blackstripes/Ignitron/docs/PROJECT_PLAN.md

# Spark Foot Controller Project Plan

This fork is being used as the software base for a standalone DIY foot controller for Positive Grid Spark amps, with the Spark 2 as the primary target. The goal is a polished, no-phone/no-computer playing experience while preserving Ignitron's proven Spark BLE/protocol work.

## Current status

The authoritative development branch is `main`. New Codex and Astra sessions
must start from `main`. `feature/headless-serial-cli` is historical branch
history and is retained temporarily for rollback/reference only.

`main` contains the `panelan-lvgl-controller` touchscreen controller path used
to exercise the Spark protocol without the legacy buttons, LEDs, or OLED.
Hardware verification now covers PanelLan display/touch, direct Spark BLE,
Home/Preset and confirmed FX actions, Device identity/serial, reconnect, and
the Spark 2 native tuner (external observation plus display entry/exit and
fresh note/cents rendering). Spark 2 preset and FX core reliability have both
passed 500-action acceptance. Current priority is completing the remaining mini
displays, switches, wiring, power/decoupling, and physical controller
integration. FX confirmation latency optimization is deliberately deferred until
after that hardware/UI bring-up; see
[DEFERRED_FX_LATENCY_OPTIMIZATION.md](DEFERRED_FX_LATENCY_OPTIMIZATION.md).
Spark 2 internal looper remains unimplemented and follows the hardware priority.
See [PANELAN_PROTOTYPE.md](PANELAN_PROTOTYPE.md) and
[CODEX_HANDOFF.md](../CODEX_HANDOFF.md) for live status.

The upstream Ignitron code is built around classic ESP32 targets and uses NimBLE for Spark communication. The final controller hardware will be ESP32-S3-based, so there will be a deliberate port step rather than assuming the stock target is drop-in compatible.

## Product goal

Build a standalone floor controller that connects directly to a Spark 2 over BLE and provides:

- Preset/bank selection
- Individual FX toggles
- Spark 2 internal looper control
- Tuner UI
- Tap tempo
- Dynamic per-switch labels/status
- A larger contextual main display
- Optional expression pedal inputs later
- USB power first; battery power can be added later

The finished controller should not require the Spark mobile app for normal Spark 2 use.

## Hardware direction

### Main controller/display board

The intended prototype/final controller board has now been positively identified from the PCB markings as:

- **PanelLan ZX2D80CE02S V1.0**
- PanelLan board family / model: **SC05_X / ZX2D80CE02S**
- Module marking: **WT32-S3-WROVER**
- MCU family: **ESP32-S3**
- Main display: **2.8-inch 240x320 IPS TFT**
- Main LCD controller: **ST7789**
- LCD bus: **8-bit 8080 parallel**, not SPI
- Touch: **FT5x06 capacitive touch**
- Existing PanelLan Arduino support is available and is based on **LovyanGFX**

Important implementation note: **do not treat the built-in display as a generic SPI ST7789 module.** Start from the known PanelLan `SC05_X` / `ZX2D80CE02S` board configuration and vendor/library support rather than inventing a pin map from scratch.

The rear expansion connector is visibly labeled:

```text
+5V
GND
IO10
IO11
IO12
IO13
IO14
IO21
```

That gives six user-accessible GPIOs for the pedal hardware. The current tentative allocation is:

```text
IO10  Mini TFT SPI MOSI
IO11  Mini TFT SPI SCLK
IO12  I2C SDA
IO13  I2C SCL
IO14  Shared mini-TFT DC
IO21  Spare / reserve
```

On I2C, the current plan is:

```text
IO12/IO13
   |-- MCP23017  -> footswitch inputs and/or six mini-TFT CS lines
   `-- ADS1115   -> future expression pedal inputs
```

The six ST7735S mini TFTs should share SPI clock/data. The MCP23017 can drive six individual CS lines directly unless a decoder later proves simpler in software/hardware.

The board's built-in display/touch use their own onboard connections, so the external IO10-IO14/IO21 pins are intended to remain available for external hardware. Still verify all details against the exact vendor board support files during the S3 port.

Before finalizing firmware pin definitions, Codex should:

- Pull the exact PanelLan SC05_X / ZX2D80CE02S board config from the maintained support package.
- Verify flash/PSRAM size and board build flags from the actual library/example.
- Verify touch-controller pins and LCD bus config from the vendor/library source.
- Confirm USB serial behavior on the physical board.
- Confirm the external IO connector pin assignments electrically before wiring all peripherals.
- Keep board-specific pin definitions isolated in a dedicated hardware config.

### Per-switch displays

Six purchased modules:

- 0.96-inch IPS TFT
- 80x160 / 160x80
- ST7735S
- SPI
- 7-pin breakout
- 3.3 V

These are intended to sit above the six primary footswitches and dynamically show labels such as `P1`, `DELAY`, `REC/DUB`, `UNDO`, etc.

Plan to share SPI clock/data across all six displays and give each display independent selection. Candidate approaches:

1. MCP23017 drives six CS signals directly.
2. A 3-to-8 active-low decoder drives CS lines, with selection controlled either by native GPIO or the MCP23017.

Given the confirmed six-pin external GPIO budget on the PanelLan board, direct CS control from the MCP23017 is currently the preferred starting point. The mini displays should be treated as write-only if possible; no MISO is expected to be required.

### Footswitches

Six purchased main switches:

- DaierTek PBS-24-302 style
- Momentary SPST
- 12 mm metal stomp switches

Current UX direction is **six primary switches plus two utility switches**:

- `MODE`
- `TAP / TUNER`

The exact utility-switch hardware can be selected later.

### GPIO expansion

A Waveshare MCP23017 breakout is planned for switch inputs and/or display chip selects.

Preferred switch electrical model:

- MCP23017 at 3.3 V
- Inputs use pull-ups
- Switches connect input to GND
- HIGH = idle, LOW = pressed

Interrupt support is optional; simple polling is acceptable initially.

### Power

USB 5 V is the initial power source.

Purchased 5 V -> 3.3 V mini buck modules can supply the six small TFTs and other 3.3 V peripherals. Verify actual output voltage with a meter before connecting displays. Do not assume the advertised current rating is a safe continuous rating without testing.

Add sensible local/bulk decoupling. Battery support is intentionally deferred until the USB-powered prototype is stable.

### Expression pedals — later phase

Possible future hardware:

- ADS1115 on I2C
- Two TRS expression jacks
- Series resistance/filtering/protection
- Tip/ring polarity configurable because expression pedals are not universal

Important: **continuous volume/wah control is not yet proven at the Spark protocol level.** Ignitron exposes parameter-change mechanisms, but the correct live parameter mapping still needs to be identified before expression support is promised.

## Physical UX direction

Use the Line 6 HX Stomp XL as inspiration for visual hierarchy and foot-control ergonomics, but keep the controller simpler.

Preferred layout: a **3 x 2 matrix of six primary switches** with a mini TFT above each switch, a larger main screen above the grid, and two dedicated utility switches.

Proposed behavior:

### Preset mode

```text
P1       P2       P3
P4       BANK-    BANK+
```

### FX mode

```text
GATE     COMP/WAH DRIVE
MOD      DELAY    REVERB
```

### Looper mode

Example only; final behavior should follow verified Spark 2 looper functions:

```text
REC/DUB  PLAY/STOP  UNDO/REDO
CLEAR    STATUS/TAP CONFIG
```

`MODE` should cycle among the useful controller modes without relying heavily on long presses.

`TAP / TUNER` should preferably use:

- short press: tap tempo
- long press: tuner

The main display should show context rather than simply duplicate the mini labels: active bank/preset, preset name, connection state, active FX, looper state, tuner, and later expression state.

No rotary encoders are planned initially. The main screen is touch-capable and the Spark app remains available for deep tone editing. Add an encoder only if a concrete interaction later justifies it.

## Enclosure direction

Prefer a 3D-printed enclosure rather than a hand-cut metal faceplate.

Target a compact sloped enclosure that can fit on a Bambu P1P 256 x 256 mm build plate. A rough concept of 9-10 inches wide by 6-7 inches deep has been discussed, but **final CAD dimensions must wait for physical measurement of all boards and switches.**

Design considerations:

- PETG or ASA preferred over brittle PLA for the final unit
- Reinforced/ribbed top around stomp switches
- Heat-set inserts for serviceable assembly
- Recess/protect all displays so stomp loads never transfer into PCBs
- Keep wiring/service access practical

Before CAD, make a full-scale cardboard/paper layout and physically test foot spacing.

## Software architecture direction

The finished code should avoid mixing Spark protocol logic, UI rendering, and physical button handling.

Preferred separation:

1. **Spark transport/protocol layer**
   - Preserve Ignitron's working BLE/protocol implementation as much as possible.
   - Avoid unnecessary rewrites.

2. **Controller state layer**
   - Amp connected/disconnected
   - Amp identity
   - Bank/preset and preset name
   - FX state
   - Looper state/config
   - Tuner note/offset/state
   - Tap/BPM
   - Future expression state

3. **Input/action layer**
   - Footswitch events
   - Touch events
   - Serial CLI commands
   - Maps user actions onto protocol operations

4. **Renderer layer**
   - Main TFT renderer
   - Six mini-TFT renderer(s)
   - Headless/serial renderer for development/debugging

5. **Hardware abstraction/configuration**
   - Board pin definitions
   - Display bus/select implementation
   - MCP23017
   - Future ADS1115

Keep the serial CLI in the finished firmware as a development/service interface even after physical controls are working.

## Serial/headless development mode

The serial CLI is an existing service/diagnostic path. Keep it available while
touch and future physical controls mature; it is the first place to probe an
unverified Spark capability without inventing UI behavior.

Desired serial commands include at least:

```text
help
status
amp
refresh
preset 1
preset 2
preset 3
preset 4
bank up
bank down
fx gate toggle
fx comp toggle
fx drive toggle
fx mod toggle
fx delay toggle
fx reverb toggle
tuner on
tuner off
tap
loop rec
loop dub
loop play
loop stop
loop undo
loop redo
loop clear
```

The serial interface should return useful success/failure/status output and should not block the BLE processing loop.

Headless mode must not require an OLED, LEDs, or physical buttons to boot. Stock Ignitron display initialization can halt forever when the expected OLED is absent, so display initialization must be bypassed cleanly in this mode.

## Spark 2 functional target

The Spark 2 is the primary supported amp for this project.

Current functional checkpoint after a successful BLE connection:

1. Read amp identity / serial / current preset state — verified.
2. Change hardware preset — verified.
3. Read/update FX state — verified for the PanelLan action path.
4. Enter/exit tuner and display fresh note/cents data — verified on Spark 2.
5. Exercise Spark 2 internal looper commands/status — pending.
6. Verify reconnect behavior after amp/controller restart — ongoing matrix.

The controller should use Ignitron's normal APP-mode/direct BLE path for Spark 2.

## Spark NEO Core investigation

Ignitron explicitly supports the original Spark NEO. NEO support was added before Spark NEO Core was released.

Positive Grid describes NEO and NEO Core as sharing the same amp modeling/effects/Spark app integration, while Core omits the NEO wireless transmitter feature. This makes NEO Core support plausible, but **it has not been confirmed in Ignitron and must not be treated as guaranteed.**

Once the controller can connect to Spark 2, perform a minimal NEO Core compatibility test:

1. BLE scan and identify advertised device/name/services.
2. Attempt Ignitron APP-mode connection.
3. Request serial/amp identity.
4. Request current preset.
5. Change preset.
6. Test one FX toggle.

If the NEO Core advertises a different name but uses the same Spark app protocol, add the smallest possible compatibility adjustment rather than creating a separate architecture.

## ESP32-S3 port constraints

The final controller is expected to use ESP32-S3 on the identified PanelLan ZX2D80CE02S / SC05_X board.

Important differences from classic ESP32:

- S3 supports BLE but not Bluetooth Classic.
- Direct Spark APP-mode BLE is the path we care about.
- Ignitron features relying on Bluetooth Classic serial are not a requirement for this controller.
- Review ESP-specific MAC manipulation, BLE keyboard code, core pinning/task assumptions, filesystem configuration, and library versions during the port.
- The onboard ST7789 is connected by **8-bit 8080 parallel**, so reuse the PanelLan/LovyanGFX support path rather than adapting generic SPI-ST7789 code.

Do not entangle the first S3 bring-up with all displays and switches at once.

## Archived initial development sequence

Milestones 1–5 below describe the completed initial port/LVGL rollout and are
kept for context. The active sequence is the looper-first plan in
`CODEX_HANDOFF.md` and the "Immediate Codex task" section below.

### Milestone 1 — stabilize the current headless implementation on main

- Review the current `main` implementation and its recent history.
- Build `esp32dev-headless` with PlatformIO.
- Fix compile/link issues.
- Ensure headless boot does not touch OLED/button/LED hardware.
- Ensure BLE processing is never blocked by CLI input.
- Keep upstream behavior unchanged for normal/non-headless builds where practical.

### Milestone 2 — PanelLan board bring-up

- Use the exact `ZX2D80CE02S / SC05_X` board support rather than a generic ESP32-S3 display profile.
- Run the vendor/demo firmware first.
- Confirm main TFT, FT5x06 touch, USB serial, flash/PSRAM.
- Record the exact support-package version and board config used.
- Confirm the exposed connector pins IO10, IO11, IO12, IO13, IO14, IO21.
- Create a board-specific config instead of scattering GPIO numbers through the code.

### Milestone 3 — ESP32-S3 protocol bring-up

- Get the project compiling for the exact PanelLan board.
- Start with serial + BLE only.
- Scan for Spark 2.
- Connect and run the functional target sequence above.
- Do not start custom UI work until direct Spark control is stable.

### Milestone 4 — NEO Core compatibility test

- Run the minimal NEO Core test sequence.
- Document exact findings and any code differences required.

### Milestone 5 — main display UI (completed foundation)

- Use the PanelLan/LovyanGFX support path for the onboard 2.8-inch ST7789 parallel TFT and FT5x06 touch.
- Start with connection/preset/FX/tuner/looper status.
- Keep the protocol layer independent from the graphics library.

### Milestone 6 — six mini displays + switch expander

- Mini display #1 (top-left) is now hardware-tested in the integrated controller
  using the SPI2 renderer; it follows the touchscreen Preset (`P1`) and FX
  (`GATE`) views. The GPIO bit-bang renderer remains an explicit fallback.
- Next, validate shared hardware SPI with all six ST7735S displays and provide
  each panel an independent chip-select, likely through the planned MCP23017.
- Add MCP23017 switch inputs and display selection.
- Current tentative native pins are IO10=MOSI, IO11=SCLK, IO12/13=I2C, IO14=shared DC, IO21=spare.
- Only after the electrical approach is stable should all six displays be connected.

### Milestone 7 — final interaction model

- Implement Preset / FX / Looper modes.
- Implement MODE and TAP/TUNER utilities.
- Minimize obscure long-press behavior.
- Make mini labels/state obvious from standing height.

### Milestone 8 — enclosure

- Measure actual hardware.
- Make a full-size physical layout mockup.
- CAD and print a prototype enclosure.
- Iterate ergonomics before final cosmetic print.

### Later milestone — expression inputs

- Add ADS1115/TRS hardware.
- Reverse-engineer/verify the relevant Spark live parameter mapping.
- Only then implement volume/wah behavior.

## Development rules / guardrails

- Preserve upstream Spark protocol code unless there is a demonstrated reason to change it.
- Do not claim NEO Core support until tested.
- Do not claim expression-wah support until the live parameter mapping is verified.
- Use the exact PanelLan board support for the main display/touch rather than generic assumptions.
- Keep final board pins isolated in board-specific config and verify them against the physical unit/vendor source.
- Prefer incremental hardware bring-up: one subsystem at a time.
- Keep serial diagnostics available throughout development.
- Maintain clear compile-time or board-specific separation so upstream classic ESP32 builds are not accidentally broken.

## Core reliability status and deferred optimization

The Spark 2 preset 500/500 and FX 500/500 core-control acceptance gates are
complete; evidence is summarized in
[SPARK_RECEIVE_FRAMING.md](SPARK_RECEIVE_FRAMING.md) and
[FX_DIRECT_CONFIRMATION_INVESTIGATION.md](FX_DIRECT_CONFIRMATION_INVESTIGATION.md).
The remaining FX confirmation-latency optimization is deliberately deferred
until after physical mini-display/switch hardware integration. Preserve the
accepted ControllerState/ControllerActions authority and confirmation model;
do not change deadlines, retry cadence, or BLE settings during hardware bring-up.
See [DEFERRED_FX_LATENCY_OPTIMIZATION.md](DEFERRED_FX_LATENCY_OPTIMIZATION.md)
for the evidence and resume checklist.

## Immediate Codex task

The main touchscreen framework is **LVGL 9.x** over the working
PanelLan/LovyanGFX path; that bring-up and the first polished screens are
complete. The immediate priority is physical controller integration:

1. Complete shared SPI and independent chip-select integration for all six mini
   TFTs, visually validating every panel.
2. Complete switch-expander and physical switch wiring, checking each input and
   display-to-switch mapping.
3. Verify power distribution, 3.3 V regulation, decoupling, wiring clearance,
   and stable operation with the physical controller integrated.
4. Keep the existing 2.8-inch UI frozen until all six mini displays work.
5. After the physical hardware gate, resume capability-gated Spark 2 looper
   state/actions and tap-tempo work through the canonical controller boundary.

Do not resume the deferred FX latency optimization until this hardware/UI
bring-up is complete.

The six future ST7735S displays remain simple state-driven renderers and should not each run their own LVGL UI.

The current Codex start instructions are maintained in the repository root [CODEX_HANDOFF.md](../CODEX_HANDOFF.md).

## UI / UX design target

### User sequencing constraint

- Keep the current 2.8-inch touchscreen UI visually/functionally frozen while
  bringing up the six mini displays. Do not redesign or update the main-panel
  UI until all six mini displays are connected and working.
- Mini #1's hardware-SPI card may take visual cues from the user-provided
  `~/Desktop/Ignitron/miniUI.png`, `miniUI2.png`, and `miniUI3.png` now;
  the full six-panel concept, physical mode/utility mappings, and remaining
  five mini UIs stay staged until the six-display hardware gate.
- Treat a future 2.8-inch UI refresh as a separate later milestone, after the
  six-display hardware gate; do not let that redesign block the current mini
  bring-up.

The detailed implementation target for the touchscreen and future mini displays is maintained in [UI_DESIGN.md](UI_DESIGN.md).

The visual concept is stored at [images/ignitron-ui-concept.jpg](images/ignitron-ui-concept.jpg).

The main touchscreen framework is **LVGL 9.x** on top of the existing PanelLan/LovyanGFX hardware path; see [LVGL_ARCHITECTURE.md](LVGL_ARCHITECTURE.md).

Key direction:

- Treat the controller as a performance instrument, not a generic settings UI.
- Main display provides performance context: preset, FX, looper, tuner, and device/connection state.
- Six mini TFTs eventually provide dynamic per-footswitch labels and state.
- Main touchscreen remains a complete control/debug fallback.
- Prioritize truthful Spark-synchronized state, large touch targets, standing-height readability, and a dark stage-friendly visual hierarchy.
- Implement device-capability awareness so Spark-2-only controls are hidden or disabled on other devices.
- Use reusable LVGL components/theme for the main display.
- Keep future mini displays lightweight and state-driven rather than running separate LVGL stacks.
- Build incrementally: verified looper protocol -> canonical looper state/actions
  -> truthful Looper UI -> interoperability matrix -> physical controls.

## Detailed behavior specifications

The product roadmap is backed by explicit implementation contracts:

- [STATE_MODEL.md](STATE_MODEL.md) defines canonical state, authority, pending/confirmed/stale semantics, capabilities, device switching, and reconnect behavior.
- [INTERACTION_SPEC.md](INTERACTION_SPEC.md) defines exact behavior for presets, FX, tuner, tempo, looper, MODE, TAP/TUNER, touchscreen, physical switches, mini TFTs, and CLI.
- [AMP_BEHAVIOR.md](AMP_BEHAVIOR.md) distinguishes amp-native logic from controller logic and contains the hardware verification matrix.
- [UI_DESIGN.md](UI_DESIGN.md) defines visual hierarchy and screen behavior.
- [LVGL_ARCHITECTURE.md](LVGL_ARCHITECTURE.md) defines the main-screen UI framework, buffering/tasking rules, reusable components, rollout checkpoints, and model/review workflow.

Central design principle: rely on native Spark behavior whenever possible.

For example, Spark 2 handles tuner mute itself. The controller should send the native tuner command and reflect confirmed state rather than turning off all effects or synthesizing a mute/restore sequence.

Unknown interactions must be tested on hardware and documented in AMP_BEHAVIOR.md before being encoded as product behavior.
