blackstripes/Ignitron/src/SparkDataControl.h

/*
 * SparkDataControl.h
 *
 *  Created on: 19.08.2021
 *      Author: stangreg
 */

#ifndef SPARKDATACONTROL_H_
#define SPARKDATACONTROL_H_

#include "CircularBuffer.h"
#include "Config_Definitions.h"
#include "SparkBLEKeyboard.h"
#include "SparkBTControl.h"
#include "SparkKeyboardControl.h"
#include "SparkLooperControl.h"
#include "SparkOutbound.h"
#include "SparkResponseLane.h"
#include "SparkTransportTelemetry.h"
#include "SparkRetainedIntents.h"
#include "SparkSubmission.h"
#include "AmpBatteryPoll.h"

#include <Arduino.h>
#include <atomic>
#include <freertos/semphr.h>
#include <queue>
#include <stdexcept>
#include <vector>

#include "SparkDisplayControl.h"
#include "SparkMessage.h"
#include "SparkPresetBuilder.h"
#include "SparkPresetControl.h"
#include "SparkStreamReader.h"

#include "SparkTypes.h"
#include "controller/ProtocolObservations.h"

using namespace std;
using ByteVector = vector<byte>;

class SparkBTControl;
class SparkDisplayControl;

class SparkDataControl {
public:
    SparkDataControl();
    virtual ~SparkDataControl();

    OperationMode init(OperationMode opMode);
    void resetStatus();
    void setDisplayControl(SparkDisplayControl *display);
    bool checkBLEConnection();
    static bool isAmpConnected();
    // Monotonic final-ACK observation for the controller action boundary.
    // It is dispatch metadata, not confirmation of amp-owned state.
    static uint32_t finalAckRevision();
    static AckData lastFinalAck();
    static bool nextFinalAck(uint32_t &cursor, AckData &ack);
    static uint32_t hardwareNumberRevision();
    static bool nextHardwareNumber(uint32_t &cursor, uint8_t &number, uint8_t &cmd,
                                   uint8_t &subcmd, uint8_t &messageNumber);
    // Monotonic, model-specific observation generation. This advances only
    // when an incoming FX_ONOFF message for the requested Spark model has
    // been applied to SparkPresetControl; it is not a command/ACK revision.
    static uint32_t fxModelObservationRevision(const string &fxName);
    // Advances only after a complete MSG_TYPE_PRESET response has been
    // applied to SparkPresetControl. ACKs and local pending mutations do not
    // affect this authoritative observation generation.
    static uint32_t fullPresetObservationRevision();
    // Protocol message number paired with the most recently applied,
    // non-background full-preset observation.
    static uint8_t fullPresetObservationMessageNumber();
    // First queued BLE notification after the latest successfully dispatched
    // query (not necessarily a reply to it). Valid even after lane completion.
    static bool firstQueryNotification(uint8_t messageNumber, uint32_t &atMs);
    // PanelLan active-preset refresh barrier; zero revokes older replies.
    static void expectControllerFullPreset(uint8_t messageNumber);
    // Incoming Spark looper observations only. These never advance for an
    // outgoing command or its transport ACK.
    static uint32_t looperStatusObservationRevision();
    static uint32_t looperSettingsObservationRevision();
    static uint32_t looperCommandObservationRevision();
    // Compact, monotonic diagnostics counters. These are intentionally
    // payload-free so they are safe to inspect on a live serial connection.
    static void recordBleDisconnect();
    static void recordBleReconnect();
    static void recordIngressDropBusy();
    static void recordIngressDropFull();
    static void recordCompletedFullPreset();
    static void recordControllerPresetSend();
    static void recordControllerPresetConfirm();
    static void recordControllerPresetFailure();
    static void recordControllerFxSend();
    static void recordControllerFxConfirm();
    static void recordControllerFxFailure();
    static void recordTransportRetry(); // an attempted semantic verification replacement
    static void printDiagnostics();
    static bool isAppConnected(); // true if ESP in AMP mode and client is connected
    void startBLEServer();
    // static void onScanEnded(NimBLEScanResults results);

    // Callback function when Spark notifies about a changed characteristic
    static void bleNotificationCallback(NimBLERemoteCharacteristic *pRemoteCharacteristic,
                                        uint8_t *pData, size_t length, bool isNotify);

    static void queueMessage(ByteVector &blk);
    // methods to process any data from Spark (process with SparkStreamReader and send ack if required)
#ifdef PANELAN_PRESET_TRACE
    static void processSparkData(ByteVector &blk, uint32_t ingressId = 0);
#else
    static void processSparkData(ByteVector &blk);
#endif

    // Check if a preset has been updated (via ack or from Spark)
    void checkForUpdates();
    // Low-priority periodic query: caller confirms foreground is ready after actions.
    void serviceBackgroundQueries(bool foregroundReady);

    static bool getAmpName();
    static bool getCurrentPresetNum(uint8_t *messageNumber = nullptr);
    static bool getSerialNumber();
    static void requestSerialNumber();
    static void requestCurrentPresetRefresh();
    static SparkSubmission lastSubmissionStatus();
#ifdef PANELAN_PRESET_TRACE
    struct PresetTransportTrace {
        SparkSubmission submission;
        bool commandHasRemaining;
        int commandRemainingParts;
        bool responseLaneActive;
        uint8_t ownerMessage, ownerSubcommand, controllerFullPresetMessageNumber;
    };
    static PresetTransportTrace presetTransportTrace();
#endif
    // Services the 5s transport deadline before testing this exact owner.
    static bool responseQueryPending(uint8_t messageNumber, uint8_t subcmd);
    static bool getFirmwareVersion();
    static bool getHWChecksums();
    bool getCurrentPreset(int num);
    static bool getCurrentPresetFromSpark(uint8_t *messageNumber = nullptr);
    static bool readHWPreset(int num);
    static void cancelHWPresetRead();

    // Switch to a selected preset of the current bank
    bool switchPreset(int pre, bool isInitial);
    bool changeHWPreset(int preset, uint8_t *messageNumber = nullptr);
    bool changePreset(Preset preset);

    // Switch effect on/off
    // Optionally returns the message number assigned to this effect command,
    // so the controller can recognize its serialized action's final ACK.
    static bool switchEffectOnOff(const string &fxName, bool enable, uint8_t *messageNumber = nullptr);
    static bool toggleEffect(int fxIdentifier);

    bool toggleSubMode();
    bool toggleLooperAppMode();

    uint8_t lastKeyboardButtonPressed() const { return lastKeyboardButtonPressed_; }
    string lastKeyboardButtonPressedString() const { return lastKeyboardButtonPressedString_; }
    KeyboardMapping &currentKeyboard() const { return keyboardControl->getCurrentKeyboard(); }
    KeyboardMapping nextKeyboard() {
        keyboardChanged_ = true;
        return keyboardControl->getNextKeyboard();
    }

    KeyboardMapping previousKeyboard() {
        keyboardChanged_ = true;
        return keyboardControl->getPreviousKeyboard();
    }

    void resetKeyboardChangeIndicator() { keyboardChanged_ = false; }

    const bool ampNameReceived() const { return ampNameReceived_; }

    const OperationMode &operationMode() const { return operationMode_; }
    OperationMode &operationMode() { return operationMode_; }

    SparkLooperControl &looperControl() { return looperControl_; }

    bool &isInitBoot() { return isInitBoot_; }

    const BTMode currentBTMode() const { return currentBTMode_; }

#ifdef ENABLE_BATTERY_STATUS_INDICATOR
    const BatteryLevel batteryLevel() const { return batteryLevel_; }
#endif

    // Set/get button mode
    const SubMode &subMode() const { return subMode_; }
    SubMode &subMode() { return subMode_; }

    bool &keyboardChanged() { return keyboardChanged_; }

    int getMaxChunkSize(int direction);
    int getMaxBlockSize(int direction);

    // Functions for Spark AMP (Server mode)
    // void receiveSparkWrite(const ByteVector& blk);
    static void switchSubMode(SubMode subMode);
    void toggleBTMode();

    bool sparkLooperCommand(LooperCommand command);
    bool sparkLooperStopAll();
    bool sparkLooperStopPlaying();
    bool sparkLooperPlay();

    bool sparkLooperRec();
    bool sparkLooperDub();
    bool sparkLooperRetry();
    bool sparkLooperStopRec();
    bool sparkLooperUndo();
    bool sparkLooperRedo();
    bool sparkLooperDeleteAll();
    bool sparkLooperStopRecAndPlay();

    bool sparkLooperPlayStop();
    bool sparkLooperRecDub();
    bool sparkLooperUndoRedo();

    bool sparkLooperGetStatus();
    bool sparkLooperGetConfig();
    bool sparkLooperGetRecordStatus();
    // One-shot internal refresh, retained until each query is dispatched.
    static void requestLooperSync();
    static void requestLooperStatus();
    static void requestLooperRecordStatus();

    void tapTempoButton();

    static bool switchTuner(bool on);

    static bool processAction();
    const SparkStreamReader &getSSR() const { return sparkSsr; }
    // Functions for Looper/Keyboard mode
    void sendButtonPressAsKeyboard(keyboardKeyDefinition key);
    void resetLastKeyboardButtonPressed();

    void restartESP(bool resetSparkMode = false);

#ifdef ENABLE_BATTERY_STATUS_INDICATOR
    // Battery level
    void updateBatteryLevel();
#endif

private:
    static OperationMode operationMode_;

    static SparkBTControl *bleControl;
    static SparkStreamReader sparkSsr;
    static SparkStatus &statusObject;
    static SparkMessage sparkMsg;
    static SparkDisplayControl *sparkDisplay;
    static SparkKeyboardControl *keyboardControl;
    static SparkLooperControl looperControl_;

    static SparkBLEKeyboard bleKeyboard;

    // TODO: Put settings into proper config file
    string btModeFileName = "/config/BTMode.config";
    string sparkModeFileName = "/config/SparkMode.config";

    // Button data
    static SubMode subMode_;
    uint8_t lastKeyboardButtonPressed_ = 0;
    string lastKeyboardButtonPressedString_ = "";
    bool keyboardChanged_ = false;

    unsigned long lastTapButtonPressed_ = 0;
    const int tapButtonThreshold_ = 2000;
    static int tapEntrySize;
    static CircularBuffer tapEntries;
    static bool recordStartFlag;

    static bool ampNameReceived_;
    unsigned int lastAmpBatteryUpdate = 0;               // When battery level was last updated
    AmpBatteryPoll ampBatteryPoll_;

    // static LooperSetting *looperSetting_;

    // Messages to send to Spark
    static vector<CmdData> currentMsg;
    static vector<CmdData> ackMsg;
    static bool customPresetNumberChangePending;
    static bool customPresetNumberChangeReady_;

    // Spark AMP mode

    static BTMode currentBTMode_;
    static OperationMode sparkModeAmp;
    static OperationMode sparkModeApp;
    ByteVector currentBTMsg;
    static AmpType sparkAmpType;
    static string sparkAmpName;
    static bool withDelay;
    static ByteVector checksums;

#ifdef ENABLE_BATTERY_STATUS_INDICATOR
    // Battery level
    static BatteryLevel batteryLevel_;
#endif

    // keep track which HW presets have been read so far
    static bool isInitBoot_;
    static byte specialMsgNum;
    static uint8_t pendingHWPresetSlot_;
    static string pendingHWPresetSerial_;
    static uint32_t linkGeneration_;
    static uint32_t pendingHWPresetLink_;
    static uint32_t pendingHWPresetChecksums_;

    static byte nextMessageNum;
#ifdef PANELAN_PRESET_TRACE
    struct QueuedIngress {
        ByteVector bytes;
        uint32_t id, atMs;
    };
    static atomic_uint32_t nextIngressId_;
    static void queueNotification(ByteVector &blk, uint32_t id, uint32_t atMs);
    static queue<QueuedIngress> msgQueue;
#else
    static queue<ByteVector> msgQueue;
#endif
    static SemaphoreHandle_t msgQueueMutex;
    static constexpr size_t kMaxQueuedNotifications = 32;
    static atomic_bool ingressInvalidated_;
    static SparkOutbound<CmdData> currentCommand;
    static SparkResponseLane responseLane_;
    static SparkTransportTelemetry telemetry_;
    static uint32_t queryTelemetryId_, writeTelemetryId_, lastMutationTelemetryId_;
    static uint32_t presetTelemetryId_, fxTelemetryId_;
    static uint32_t busySince_[2];
    static bool busySeen_[2];
    static atomic_uint32_t firstNotificationAt_;
    static uint8_t notificationQueryMessageNumber_;
    static atomic_bool notificationArmed_;
    static atomic_uint32_t ingressHighWater_;
    static SparkRetainedIntents retainedIntents_;
    static SparkSubmission lastSubmissionStatus_;
    static deque<AckData> pendingLooperAcks;
    static uint32_t finalAckRevision_;
    static AckData lastFinalAck_;
    struct HardwareNumberEvent { uint8_t number, cmd, subcmd, messageNumber; };
    static ProtocolObservations<AckData> finalAckEvents_;
    static ProtocolObservations<HardwareNumberEvent> hardwareNumberEvents_;
    static vector<pair<string, uint32_t>> fxModelObservationRevisions_;
    static uint32_t fullPresetObservationRevision_;
    static uint8_t fullPresetObservationMessageNumber_;
    static uint8_t controllerFullPresetMessageNumber_;
    static uint32_t looperStatusObservationRevision_;
    static uint32_t looperSettingsObservationRevision_;
    static uint32_t looperCommandObservationRevision_;
    static uint32_t ignoreTunerOutputUntilMs_;
    static atomic_uint32_t bleDisconnectCount_;
    static atomic_uint32_t bleReconnectCount_;
    static atomic_uint32_t ingressDropBusyCount_;
    static atomic_uint32_t ingressDropFullCount_;
    static atomic_uint32_t completedFullPresetCount_;
    static atomic_uint32_t controllerPresetSendCount_;
    static atomic_uint32_t controllerPresetConfirmCount_;
    static atomic_uint32_t controllerPresetFailureCount_;
    static atomic_uint32_t controllerFxSendCount_;
    static atomic_uint32_t controllerFxConfirmCount_;
    static atomic_uint32_t controllerFxFailureCount_;

    static bool sendMessageToBT(ByteVector &msg, size_t *chunks = nullptr);
#ifdef PANELAN_PRESET_TRACE
    static bool takeQueuedMessage(ByteVector &message, uint32_t &id, uint32_t &atMs);
#else
    static bool takeQueuedMessage(ByteVector &message);
#endif
    static void clearQueuedMessages();
    static bool triggerCommand(vector<CmdData> &msg);
    static void serviceRetainedIntents();
    static void invalidateResponseOwner();
    static void expireResponseOwner();
    static bool writeRequest(const CmdData &request);

    // Retrieves the current preset from Spark (required for HW presets)
    static void setAmpParameters();
    static void readPresetChecksums();

    // methods to process any data from Spark (process with SparkStreamReader and send ack if required)
    static void handleSendingAck(const ByteVector &blk);
    static void handleAmpModeRequest();
    static void handleAppModeResponse();
    static void handleIncomingAck();

    // Read in all HW presets
    void readOpModeFromFile();
    void readBTModeFromFile();

    static bool updateLooperSettings();
    static void startLooperTimer(void *args);
    static void updateLooperCommand(byte lastCommand);
};

#endif /* SPARKDATACONTROL_H_ */
