blackstripes/Ignitron/src/SparkPresetControl.h

#ifndef SPARKPRESETCONTROL_H
#define SPARKPRESETCONTROL_H

#include "SparkDataControl.h"
#include "SparkPresetBuilder.h"
#include "SparkStatus.h"
#include "SparkTypes.h"

enum PresetEditMode {
    PRESET_EDIT_NONE,
    PRESET_EDIT_STORE,
    PRESET_EDIT_DELETE
};

class SparkDataControl;

class SparkPresetControl {
public:
    static SparkPresetControl &getInstance();
    SparkPresetControl(const SparkPresetControl &) = delete; // Disable copy constructor
    SparkPresetControl &operator=(const SparkPresetControl &) = delete;

    void init();
    void setDataControl(SparkDataControl *dataControl) { sparkDC = dataControl; }

    // Return active or pending preset/bank, set/get active preset number
    const Preset &activePreset() const { return activePreset_; }
    const Preset &pendingPreset() const { return pendingPreset_; }
    const int &activePresetNum() const { return activePresetNum_; }
    const int &pendingPresetNum() const { return pendingPresetNum_; }

    // int& activePresetNum() {return activePresetNum_;}
    const int &activeBank() const { return activeBank_; }
    const int &pendingBank() const { return pendingBank_; }
    const int &activeHWBank() const { return activeHWBank_; }
    const int &pendingHWBank() const { return pendingHWBank_; }
    const int numberOfHWBanks() const { return presetBuilder.numberOfHWbanks(); }
    bool hardwareChecksumsReady() const { return hardwareChecksumsReady_; }
    uint32_t hardwareCacheGeneration() const { return hardwareCacheGeneration_; }
    bool isHWPresetMissing(int num) { return presetBuilder.isHWPresetMissing(num); }
    const int numberOfBanks() const { return presetBuilder.getNumberOfBanks(); }
    const Preset &appReceivedPreset() const { return appReceivedPreset_; }

    void updatePendingWithActive();
    void updateActiveWithPendingPreset();

    bool readLastPresetFromFile();
    bool writeCurrentPresetToFile();

    const bool allHWPresetsAvailable() const { return allHWPresetsAvailable_; }

    const int presetNumToEdit() const { return presetNumToEdit_; }
    const string responseMsg() const { return responseMsg_; }
    const PresetEditMode presetEditMode() const { return presetEditMode_; }

    void setAmpParameters(string ampName);

    void setBank(int i);
    void increaseBank();
    void decreaseBank();
    bool increasePresetLooper();
    bool decreasePresetLooper();
    bool switchPreset(int pre, bool isInitial);
    void updateFromSparkResponseHWPreset(int presetNum);
    void toggleFX(Pedal receivedEffect);
    // TODO: Clean up with toggleFX
    void switchFXOnOff(const string name, bool onOff);

    void updateFromSparkResponsePreset(bool isSpecial);
    void updateFromSparkResponseAmpPreset(char *presetJson);
    void updateFromSparkResponseACK();

    void processPresetEdit(int presetNum = 0);
    void resetPresetEdit(bool resetEditMode, bool resetPreset = false);
    void resetPresetEditResponse();
    bool handleDeletePreset();
    bool processPresetSelect(int presetNum);

    // get a preset from saved presets
    Preset getPreset(int bank, int pre);

    void getMissingHWPresets();
    void resetStatus();
    void checkForUpdates(int operationMode);
    void validateChecksums(vector<byte> checksums);

private:
    SparkPresetControl();
    ~SparkPresetControl();

    // PRESET variables
    Preset activePreset_;
    Preset pendingPreset_ = activePreset_;
    int activeBank_ = 0;
    int pendingBank_ = 0;
    int activePresetNum_ = 0;
    int pendingPresetNum_ = 0;
    bool allHWPresetsAvailable_ = false;
    bool hardwareChecksumsReady_ = false;
    uint32_t hardwareCacheGeneration_ = 0;
    vector<byte> validatedHWChecksums_;
    const string lastPresetFileNamePrefix = "/LastPreset";

    // HW variables
    int activeHWBank_ = 0;
    int pendingHWBank_ = 0;

    // AMP Mode presets
    Preset appReceivedPreset_;
    int presetNumToEdit_ = 0;
    int presetBankToEdit_ = 0;
    PresetEditMode presetEditMode_ = PRESET_EDIT_NONE;

    string responseMsg_ = "";

    int lastUpdateCheck = 0;
    int updateInterval = 3000;

    SparkPresetBuilder presetBuilder;
    SparkDataControl *sparkDC;
    SparkStatus &statusObject = SparkStatus::getInstance();

    string sparkPresetFileName = "/config/SparkPreset.config";

    // AMP mode preset operations
    void processStorePresetRequest(int presetNum);
    void processDeletePresetRequest();
    void setPresetDeletionFlag();
    void updatePendingBankStatus();

    static void checkForMissingPresets(void *args);
    void updatePendingPreset(int bnk);
    void setActiveHWPreset();
};

#endif
