blackstripes/Ignitron/src/SparkSerialCLI.cpp

#include "SparkSerialCLI.h"

#include "controller/ControllerActions.h"

#include "Config_Definitions.h"
#include "SparkDataControl.h"
#include "SparkPresetControl.h"
#include "SparkStatus.h"
#include "PersistentEventLog.h"

#if defined(PANELAN_SC05X_MODE) && defined(PANELAN_LVGL_UI_MODE)
#include "PanelLanLVGLUI.h"
extern PanelLanLVGLUI panelLanDisplay;
#ifdef PANELAN_MINI_COEXISTENCE_TRACE
#include "PanelLanMiniDisplay.h"
extern PanelLanMiniDisplay panelLanMiniDisplay;
#endif
#endif

SparkSerialCLI::SparkSerialCLI(SparkDataControl *dataControl, ControllerActions *controllerActions)
    : sparkDC_(dataControl), controllerActions_(controllerActions) {
}

void SparkSerialCLI::begin() {
    inputBuffer_.reserve(128);
    Serial.println();
    Serial.println("Ignitron headless serial CLI ready.");
    Serial.println("Type 'help' for commands.");
    Serial.print("> ");
}

void SparkSerialCLI::update() {
    while (Serial.available() > 0) {
        char c = static_cast<char>(Serial.read());

        if (c == '\r') {
            continue;
        }

        if (c == '\n') {
            String command = inputBuffer_;
            inputBuffer_ = "";
            command.trim();
            if (command.length() > 0) {
                execute(command);
            }
            Serial.print("> ");
            continue;
        }

        if ((c == '\b' || c == 0x7F) && inputBuffer_.length() > 0) {
            inputBuffer_.remove(inputBuffer_.length() - 1);
            continue;
        }

        if (inputBuffer_.length() < 127) {
            inputBuffer_ += c;
        }
    }
}

void SparkSerialCLI::execute(String command) {
    command.trim();
    command.toLowerCase();

    int firstSpace = command.indexOf(' ');
    String verb = firstSpace < 0 ? command : command.substring(0, firstSpace);
    String args = firstSpace < 0 ? "" : command.substring(firstSpace + 1);
    args.trim();

#ifdef PANELAN_MINI_COEXISTENCE_TRACE
    if (verb == "mini") {
        panelLanMiniDisplay.diagnosticCommand(args);
        return;
    }
#endif
    if (verb == "help" || verb == "?") {
        printHelp();
    } else if (verb == "status") {
        printStatus();
    } else if (verb == "report" || verb == "diagnostics") {
        printDiagnostics();
    } else if (verb == "log") {
        if (args == "status") persistentEventLog.printStatus(Serial);
        else if (args == "dump") persistentEventLog.dump(Serial);
        else if (args == "clear confirm") Serial.println(persistentEventLog.clear() ? "Event log cleared." : "Event log is RAM-only; nothing persisted to clear.");
        else Serial.println("Usage: log status|dump|clear confirm");
    } else if (verb == "preset") {
        handlePreset(args);
    } else if (verb == "bank") {
        handleBank(args);
    } else if (verb == "fx") {
        handleEffect(args);
    } else if (verb == "tuner") {
        handleTuner(args);
    } else if (verb == "loop" || verb == "looper") {
        handleLooper(args);
    } else if (verb == "tap") {
        sparkDC_->tapTempoButton();
        Serial.println("Tap registered.");
    } else if (verb == "amp") {
        if (!SparkDataControl::isAmpConnected()) {
            Serial.println("Spark amp is not connected.");
        } else {
            if (sparkDC_->getAmpName()) {
                sparkDC_->requestSerialNumber();
                Serial.println("Requested amp identity; serial queued after name response.");
            } else Serial.println("Amp identity not sent (transport busy or write failed); retry 'amp'.");
        }
    } else if (verb == "refresh") {
        if (!SparkDataControl::isAmpConnected()) {
            Serial.println("Spark amp is not connected.");
        } else {
            Serial.println(sparkDC_->getCurrentPresetFromSpark() ? "Requested current preset." :
                           "Current preset not sent (transport busy or write failed); retry 'refresh'.");
        }
    } else if (verb == "screenshot") {
#if defined(PANELAN_SC05X_MODE) && defined(PANELAN_LVGL_UI_MODE)
        panelLanDisplay.writeScreenshot(Serial);
#else
        Serial.println("Screenshots are available only in the PanelLan LVGL target.");
#endif
    } else if (verb == "touch") {
#if defined(PANELAN_SC05X_MODE) && defined(PANELAN_LVGL_UI_MODE)
        int split = args.indexOf(' ');
        if (split < 0) {
            Serial.println("Usage: touch <x> <y>");
        } else {
            int x = args.substring(0, split).toInt();
            int y = args.substring(split + 1).toInt();
            if (x < 0 || x >= 320 || y < 0 || y >= 240) {
                Serial.println("Touch coordinates must be within 320x240.");
            } else {
                panelLanDisplay.injectTouch(static_cast<uint16_t>(x), static_cast<uint16_t>(y));
                Serial.printf("Injected touch: %d, %d\n", x, y);
            }
        }
#else
        Serial.println("Touch injection is available only in the PanelLan LVGL target.");
#endif
    } else {
        Serial.println("Unknown command. Type 'help'.");
    }
}

void SparkSerialCLI::printHelp() {
    Serial.println("Commands:");
#ifdef PANELAN_MINI_COEXISTENCE_TRACE
    Serial.println("  mini status|pause|main|run|raw-frame|raw-reset|dynamic");
#endif
    Serial.println("  status");
    Serial.println("  report                  Print compact counters since boot (alias: diagnostics)");
    Serial.println("  log status|dump|clear confirm");
    Serial.println("  amp                     Request amp identity");
    Serial.println("  refresh                 Request current preset");
    Serial.println("  screenshot              Stream a PPM screenshot over USB serial");
    Serial.println("  touch <x> <y>           Inject one LVGL touch press/release (development)");
    Serial.println("  preset <1-8>             (model dependent)");
    Serial.println("  bank up|down");
    Serial.println("  fx <gate|comp|drive|mod|delay|reverb> <toggle|on|off>");
    Serial.println("  tuner on|off");
    Serial.println("  tuner probe on|off      Native tuner diagnostic; observe serial events/audio");
    Serial.println("  tap");
    Serial.println("  loop rec|dub|recdub|play|stop|playstop|undo|redo|undoredo|clear");
    Serial.println("  loop status|config");
    Serial.println("  help");
}

void SparkSerialCLI::printStatus() {
    SparkPresetControl &presetControl = SparkPresetControl::getInstance();
    SparkStatus &status = SparkStatus::getInstance();
    const Preset &preset = presetControl.activePreset();

    Serial.println("--- Ignitron status ---");
    Serial.printf("Spark connected: %s\n", SparkDataControl::isAmpConnected() ? "yes" : "no");

    const string ampName = status.ampName();
    const string ampSerial = status.ampSerialNumber();
    Serial.printf("Amp: %s\n", ampName.empty() ? "(unknown)" : ampName.c_str());
    Serial.printf("Serial: %s\n", ampSerial.empty() ? "(unknown)" : ampSerial.c_str());

    Serial.printf("Mode: %d  Submode: %d\n", sparkDC_->operationMode(), sparkDC_->subMode());
    Serial.printf("Bank: %d  Preset: %d\n", presetControl.activeBank(), presetControl.activePresetNum());
    Serial.printf("Active hardware slot: %d\n",
                  presetControl.activeHWBank() * PRESETS_PER_BANK + presetControl.activePresetNum());
    Serial.printf("Preset name: %s\n", preset.name.empty() ? "(unknown)" : preset.name.c_str());
    if (sparkDC_->subMode() == SUB_MODE_TUNER) {
        Serial.printf("Tuner: %s  %+d cents\n", status.noteString().c_str(), status.noteOffsetCents());
    }
    if (controllerActions_) {
        const ControllerSnapshot &snapshot = controllerActions_->snapshot();
        const char *phase = "Unknown";
        switch (snapshot.connectionPhase) {
        case ControllerConnectionPhase::Scanning: phase = "Scanning"; break;
        case ControllerConnectionPhase::Reconnecting: phase = "Reconnecting"; break;
        case ControllerConnectionPhase::Identifying: phase = "Identifying"; break;
        case ControllerConnectionPhase::Syncing: phase = "Syncing"; break;
        case ControllerConnectionPhase::Ready: phase = "Ready"; break;
        }
        Serial.printf("Controller phase: %s\n", phase);
        Serial.printf("identityKnown: %s\n", snapshot.identityKnown ? "true" : "false");
        Serial.printf("sparkStateStale: %s\n", snapshot.sparkStateStale ? "true" : "false");
        Serial.printf("fullPresetObservedForLink: %s\n", snapshot.fullPresetObservedForLink ? "true" : "false");
        Serial.printf("confirmedHardwarePreset: %u\n", snapshot.confirmedHardwarePreset);
        Serial.printf("pendingHardwarePreset: %u\n", snapshot.pendingHardwarePreset);
        Serial.printf("presetActionFailed: %s\n", snapshot.presetActionFailed ? "true" : "false");
        Serial.printf("FX chain: %s\n", snapshot.fxChainIdentity.empty() ? "(unknown)" : snapshot.fxChainIdentity.c_str());
        static constexpr const char *fxLabels[] = {"gate", "comp", "drive", "mod", "delay", "reverb"};
        for (size_t i = 0; i < snapshot.fxSlots.size(); ++i) {
            const ControllerFxSlot &slot = snapshot.fxSlots[i];
            Serial.printf("FX %s: known=%s model=%s enabled=%s pending=%s failed=%s\n",
                          fxLabels[i], slot.known ? "true" : "false",
                          slot.modelName.empty() ? "(unknown)" : slot.modelName.c_str(),
                          slot.enabled ? "true" : "false", slot.pending ? "true" : "false",
                          slot.actionFailed ? "true" : "false");
        }
    }
#ifdef PANELAN_PRESET_TRACE
    const auto transport = SparkDataControl::presetTransportTrace();
    const char *submission = transport.submission == SparkSubmission::Sent ? "Sent" :
                             transport.submission == SparkSubmission::Busy ? "Busy" : "Failed";
    Serial.printf("lastSubmissionStatus: %s\n", submission);
    Serial.printf("currentCommand hasRemaining: %s  remainingParts: %d\n",
                  transport.commandHasRemaining ? "true" : "false", transport.commandRemainingParts);
    Serial.printf("responseLane active: %s  owner msg: %u  owner sub: %02X\n",
                  transport.responseLaneActive ? "true" : "false", transport.ownerMessage,
                  transport.ownerSubcommand);
    Serial.printf("controllerFullPresetMessageNumber: %u\n", transport.controllerFullPresetMessageNumber);
#endif
    Serial.printf("Looper loops: %d\n", status.numberOfLoops());
}

void SparkSerialCLI::printDiagnostics() {
    SparkDataControl::printDiagnostics();
}

void SparkSerialCLI::handlePreset(const String &args) {
    int presetNumber = args.toInt();
    if (presetNumber < 1 || presetNumber > 8) {
        Serial.println("Usage: preset <1-8>");
        return;
    }

    if (!SparkDataControl::isAmpConnected()) {
        Serial.println("Spark amp is not connected.");
        return;
    }

    if (controllerActions_) {
        if (controllerActions_->requestHardwarePreset(static_cast<uint8_t>(presetNumber))) {
            Serial.printf("Preset %d requested.\n", presetNumber);
        } else {
            Serial.println("Preset request rejected; wait for synchronization to finish.");
        }
    } else if (SparkPresetControl::getInstance().processPresetSelect(presetNumber)) {
        Serial.printf("Preset %d selected.\n", presetNumber);
    } else {
        Serial.printf("Preset %d selection was not completed.\n", presetNumber);
    }
}

void SparkSerialCLI::handleBank(const String &args) {
    SparkPresetControl &presetControl = SparkPresetControl::getInstance();
    if (args == "up") {
        presetControl.increaseBank();
        Serial.printf("Pending bank: %d\n", presetControl.pendingBank());
    } else if (args == "down") {
        presetControl.decreaseBank();
        Serial.printf("Pending bank: %d\n", presetControl.pendingBank());
    } else {
        Serial.println("Usage: bank up|down");
    }
}

int SparkSerialCLI::effectIndex(const String &name) const {
    if (name == "gate" || name == "noisegate" || name == "noise")
        return INDEX_FX_NOISEGATE;
    if (name == "comp" || name == "compressor" || name == "wah")
        return INDEX_FX_COMP;
    if (name == "drive" || name == "od")
        return INDEX_FX_DRIVE;
    if (name == "mod" || name == "modulation")
        return INDEX_FX_MOD;
    if (name == "delay")
        return INDEX_FX_DELAY;
    if (name == "reverb" || name == "verb")
        return INDEX_FX_REVERB;
    return INDEX_FX_INVALID;
}

void SparkSerialCLI::handleEffect(const String &args) {
    int split = args.indexOf(' ');
    if (split < 0) {
        Serial.println("Usage: fx <gate|comp|drive|mod|delay|reverb> <toggle|on|off>");
        return;
    }

    String effectName = args.substring(0, split);
    String action = args.substring(split + 1);
    effectName.trim();
    action.trim();

    int index = effectIndex(effectName);
    if (index == INDEX_FX_INVALID) {
        Serial.println("Unknown effect slot.");
        return;
    }

#if defined(PANELAN_SC05X_MODE)
    if (action == "on" || action == "off") {
        Serial.println("PanelLan controller profile accepts only 'fx ... toggle'.");
        return;
    }
#endif

    if (!SparkDataControl::isAmpConnected()) {
        Serial.println("Spark amp is not connected.");
        return;
    }

    const Preset &preset = SparkPresetControl::getInstance().activePreset();
    if (preset.isEmpty || preset.pedals.size() <= static_cast<size_t>(index)) {
        Serial.println("Current preset data is not available yet. Try 'refresh'.");
        return;
    }

    bool ok = false;
    if (action == "toggle" && controllerActions_) {
        // ControllerActions uses six logical slots and omits the amp at raw
        // pedal index 3, while these CLI constants are raw preset indices.
        const uint8_t controllerSlot = index > INDEX_FX_AMP ? static_cast<uint8_t>(index - 1)
                                                             : static_cast<uint8_t>(index);
        ok = controllerActions_->requestFxToggle(controllerSlot);
    } else if (action == "toggle") {
        ok = SparkDataControl::toggleEffect(index);
    } else if (action == "on" || action == "off") {
        const string &actualEffectName = preset.pedals[index].name;
        if (actualEffectName.empty()) {
            Serial.println("Effect name is unavailable for this preset.");
            return;
        }
        ok = SparkDataControl::switchEffectOnOff(actualEffectName, action == "on");
    } else {
        Serial.println("Action must be toggle, on, or off.");
        return;
    }

    Serial.println(ok ? (controllerActions_ && action == "toggle" ? "Effect toggle requested." : "Effect command sent.")
                      : "Effect command failed or was rejected.");
}

void SparkSerialCLI::handleTuner(const String &args) {
    const int separator = args.indexOf(' ');
    const String tunerVerb = separator < 0 ? args : args.substring(0, separator);
    if (tunerVerb == "probe") {
        String probeArgs = separator < 0 ? "" : args.substring(separator + 1);
        probeArgs.trim();
        handleTunerProbe(probeArgs);
        return;
    }

    if (!SparkDataControl::isAmpConnected()) {
        Serial.println("Spark amp is not connected.");
        return;
    }

    if (args == "on") {
        sparkDC_->switchSubMode(SUB_MODE_TUNER);
        Serial.println(SparkDataControl::lastSubmissionStatus() == SparkSubmission::Sent ?
                       "Tuner command sent; awaiting Spark observation." : "Tuner command not sent; retry.");
    } else if (args == "off") {
        sparkDC_->switchSubMode(SUB_MODE_PRESET);
        Serial.println(SparkDataControl::lastSubmissionStatus() == SparkSubmission::Sent ?
                       "Tuner exit command sent; awaiting Spark observation." : "Tuner exit not sent; retry.");
    } else {
        Serial.println("Usage: tuner on|off");
    }
}

void SparkSerialCLI::handleTunerProbe(const String &args) {
    if (args != "on" && args != "off") {
        Serial.println("Usage: tuner probe on|off");
        return;
    }

    if (!SparkDataControl::isAmpConnected()) {
        Serial.println("Spark amp is not connected.");
        return;
    }

    const bool enable = args == "on";
    const bool sent = SparkDataControl::switchTuner(enable);
    if (sent) {
        Serial.printf("Native tuner diagnostic command sent (%s). Observe incoming tuner events and amp audio; Ignitron submode was not changed.\n",
                      enable ? "on" : "off");
    } else {
        Serial.println("Native tuner diagnostic command failed to send.");
    }
}

void SparkSerialCLI::handleLooper(const String &args) {
    if (!SparkDataControl::isAmpConnected()) {
        Serial.println("Spark amp is not connected.");
        return;
    }

    bool ok = false;
    if (args == "rec")
        ok = sparkDC_->sparkLooperRec();
    else if (args == "dub")
        ok = sparkDC_->sparkLooperDub();
    else if (args == "recdub")
        ok = sparkDC_->sparkLooperRecDub();
    else if (args == "play")
        ok = sparkDC_->sparkLooperPlay();
    else if (args == "stop")
        ok = sparkDC_->sparkLooperStopPlaying();
    else if (args == "playstop")
        ok = sparkDC_->sparkLooperPlayStop();
    else if (args == "undo")
        ok = sparkDC_->sparkLooperUndo();
    else if (args == "redo")
        ok = sparkDC_->sparkLooperRedo();
    else if (args == "undoredo")
        ok = sparkDC_->sparkLooperUndoRedo();
    else if (args == "clear" || args == "delete")
        ok = sparkDC_->sparkLooperDeleteAll();
    else if (args == "status")
        ok = sparkDC_->sparkLooperGetStatus();
    else if (args == "config")
        ok = sparkDC_->sparkLooperGetConfig();
    else {
        Serial.println("Usage: loop rec|dub|recdub|play|stop|playstop|undo|redo|undoredo|clear|status|config");
        return;
    }

    Serial.println(ok ? "Looper command sent." : "Looper command failed.");
}
