blackstripes/Ignitron/src/SparkStatus.h

#ifndef SPARKCURRENTSTATUS_H
#define SPARKCURRENTSTATUS_H

#include "SparkTypes.h"

enum MessageType {
    MSG_TYPE_NONE,
    MSG_TYPE_PRESET,
    MSG_TYPE_HWPRESET,
    MSG_TYPE_FX_ONOFF,
    MSG_TYPE_FX_CHANGE,
    MSG_TYPE_FX_PARAM,
    MSG_TYPE_AMP_NAME,
    MSG_TYPE_AMP_SERIAL,
    MSG_TYPE_LOOPER_SETTING,
    MSG_TYPE_TAP_TEMPO,
    MSG_TYPE_MEASURE,
    MSG_TYPE_LOOPER_COMMAND,
    MSG_TYPE_LOOPER_STATUS,
    MSG_TYPE_TUNER_OUTPUT,
    MSG_TYPE_TUNER_ON,
    MSG_TYPE_TUNER_OFF,
    MSG_TYPE_HWCHECKSUM,
    MSG_TYPE_HWCHECKSUM_EXT,
    MSG_TYPE_AMPSTATUS,
    MSG_TYPE_INPUT_VOLUME,
    MSG_REQ_SERIAL,
    MSG_REQ_FW_VER,
    MSG_REQ_PRESET_CHK,
    MSG_REQ_CURR_PRESET_NUM,
    MSG_REQ_CURR_PRESET,
    MSG_REQ_AMP_STATUS,
    MSG_REQ_72,
    MSG_REQ_PRESET1,
    MSG_REQ_PRESET2,
    MSG_REQ_PRESET3,
    MSG_REQ_PRESET4,
    MSG_REQ_INVALID,
};

class SparkStatus {
public:
    static SparkStatus &getInstance();
    ~SparkStatus();

    SparkStatus(const SparkStatus &) = delete; // Disable copy constructor
    SparkStatus &operator=(const SparkStatus &) = delete;

    // Preset related methods to make information public
    const Preset currentPreset() const { return currentPreset_; }
    Preset &currentPreset() { return currentPreset_; }

    const int currentPresetNumber() const { return currentPresetNumber_; }
    int &currentPresetNumber() { return currentPresetNumber_; }

    const boolean isPresetNumberUpdated() const { return isPresetNumberUpdated_; }
    boolean &isPresetNumberUpdated() { return isPresetNumberUpdated_; }

    const boolean isPresetUpdated() const { return isPresetUpdated_; }
    boolean &isPresetUpdated() { return isPresetUpdated_; }

    const boolean isLooperSettingUpdated() const { return isLooperSettingUpdated_; }
    boolean &isLooperSettingUpdated() { return isLooperSettingUpdated_; }

    const LooperSetting currentLooperSetting() const { return looperSetting_; }
    LooperSetting &currentLooperSetting() { return looperSetting_; }
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
